SphericalCowww/CubicDoggo_06Z/src/my_robot_description/world/forest.png

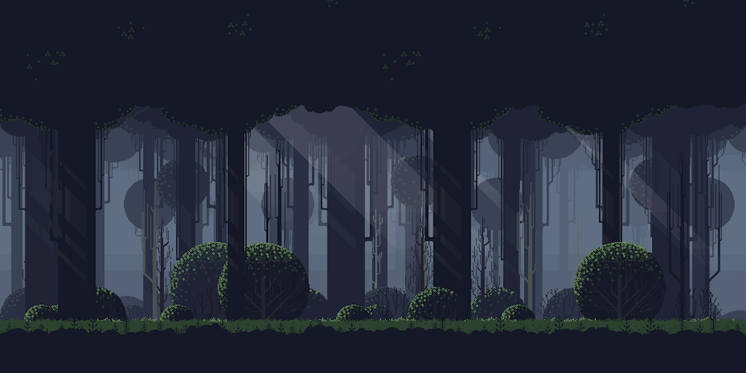
src/my_robot_description/world/forest.png
