SphericalCowww/CubicDoggo_06Z/src/my_robot_description/world/forest_pinocchio.png

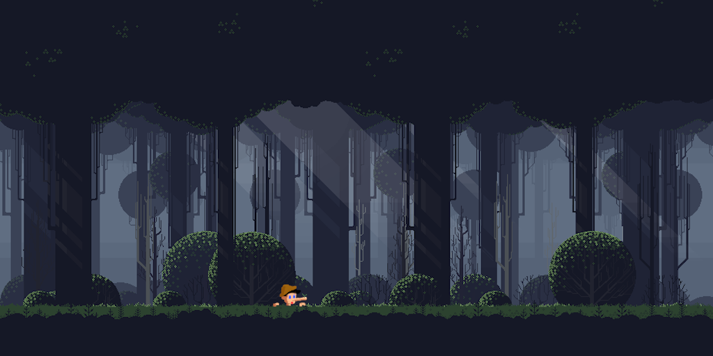
src/my_robot_description/world/forest_pinocchio.png
