SphericalCowww/CubicDoggo_06Z/src/my_robot_description/mesh/CADv3/thighInner.FCStd

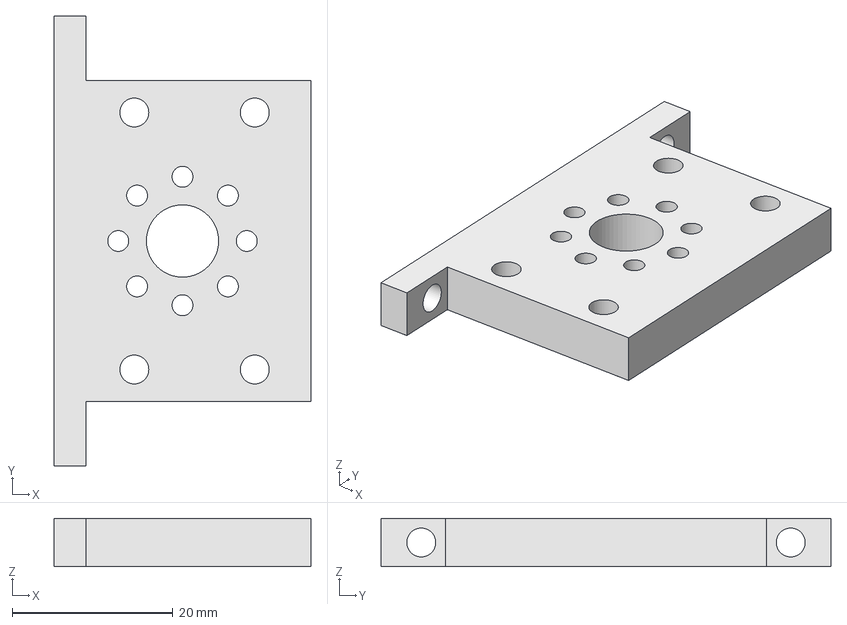
[picture p22: CAD file, 2026-09-27]
src/my_robot_description/mesh/CADv3/thighInner.FCStd
32.0 x 56.0 x 6.00 mm
