SphericalCowww/CubicDoggo_06Z/src/my_robot_description/mesh/CADv3/fanFlag.FCStd

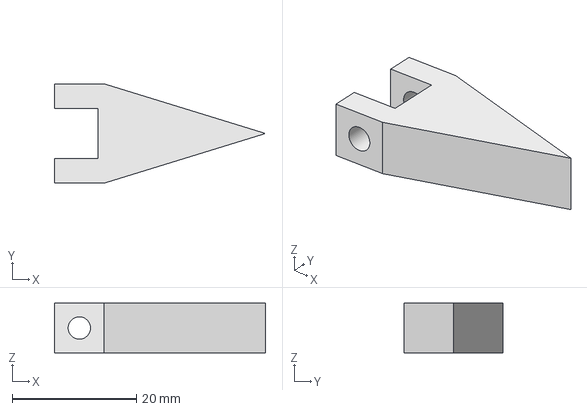
[picture p23: CAD file, 2026-09-27]
src/my_robot_description/mesh/CADv3/fanFlag.FCStd
34.0 x 16.0 x 8.00 mm
