SphericalCowww/CubicDoggo_06Z/src/my_robot_description/mesh/CADv3/baseTorso.FCStd

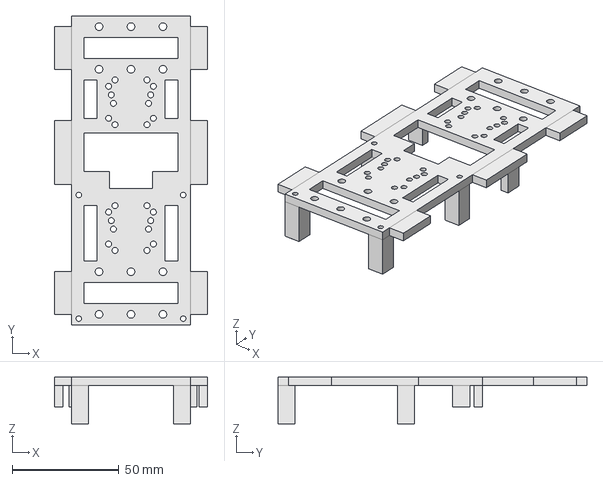
[picture p24: CAD file, 2026-09-27]
src/my_robot_description/mesh/CADv3/baseTorso.FCStd
72.0 x 145.0 x 22.0 mm
