SphericalCowww/CubicDoggo_06Z/src/my_robot_description/mesh/CADv3/XL430holderThighFront.FCStd

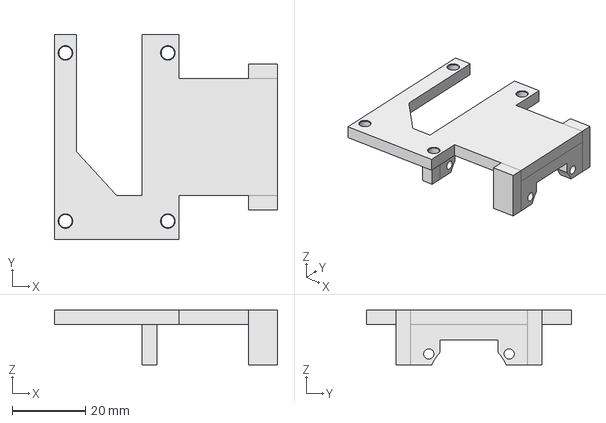
[picture p25: CAD file, 2026-09-27]
src/my_robot_description/mesh/CADv3/XL430holderThighFront.FCStd
61.0 x 56.0 x 15.0 mm
