SphericalCowww/CubicDoggo_06Z/src/my_robot_description/mesh/CADv3/hdmiHolder.FCStd

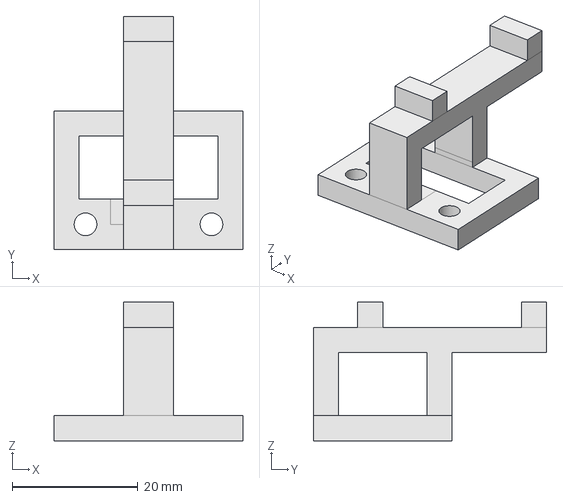
[picture p26: CAD file, 2026-09-27]
src/my_robot_description/mesh/CADv3/hdmiHolder.FCStd
30.0 x 37.0 x 22.0 mm
