SphericalCowww/CubicDoggo_06Z/src/my_robot_description/mesh/CADv3/batteryHolder.FCStd

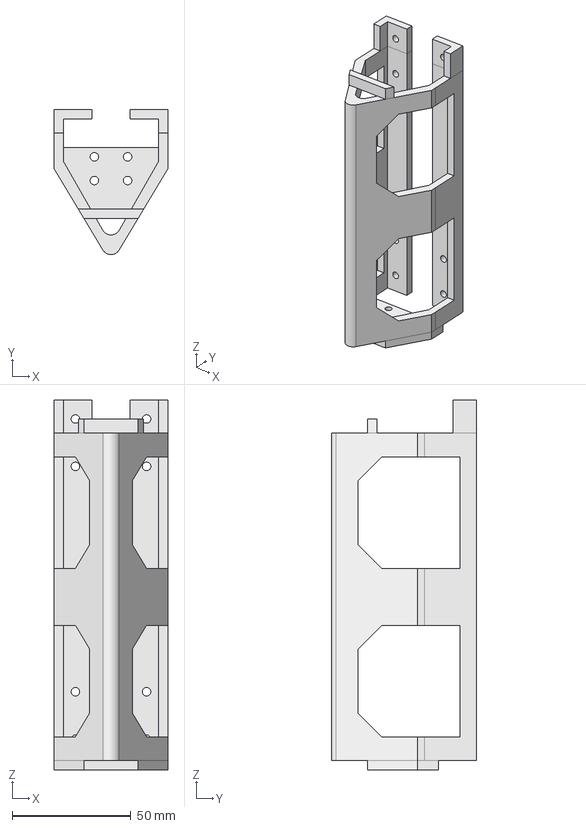
[picture p27: CAD file, 2026-09-06]
src/my_robot_description/mesh/CADv3/batteryHolder.FCStd
48.0 x 61.2 x 156.0 mm
